Alavas/Modbus_Datalogger/Photos/DSC_0623.jpg

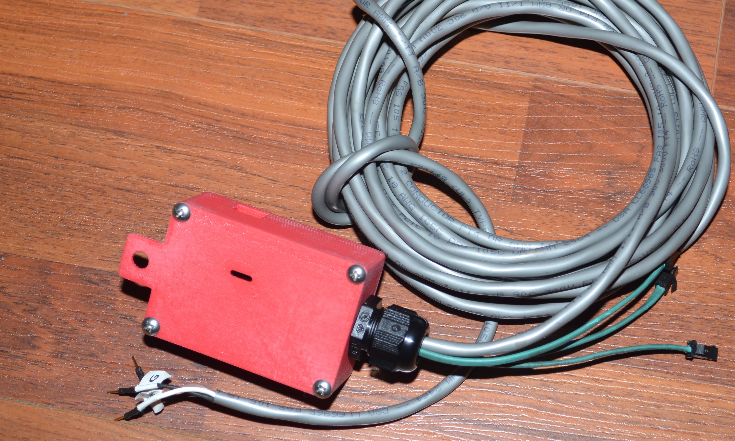
Photos/DSC_0623.jpg
