Alavas/Modbus_Datalogger/Photos/DSC_0625.jpg

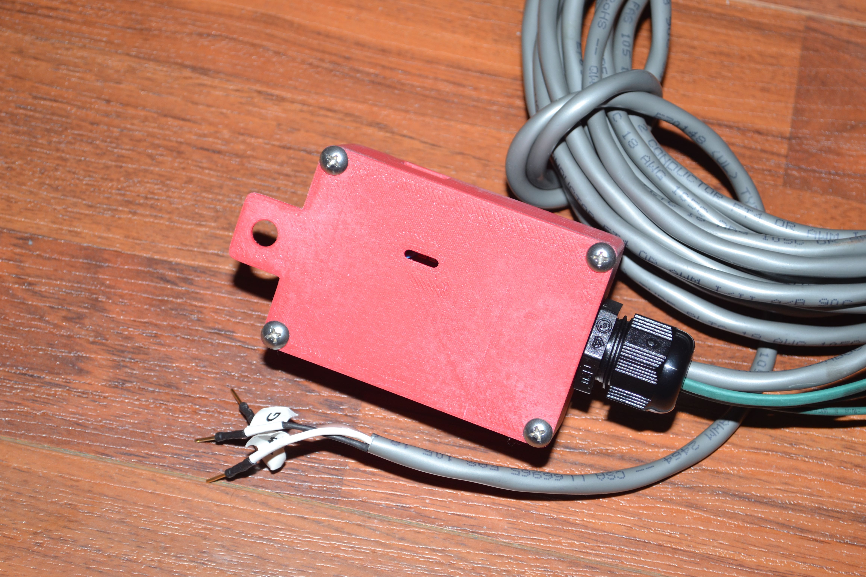
Photos/DSC_0625.jpg
