Alavas/Modbus_Datalogger/Photos/DSC_0633.jpg

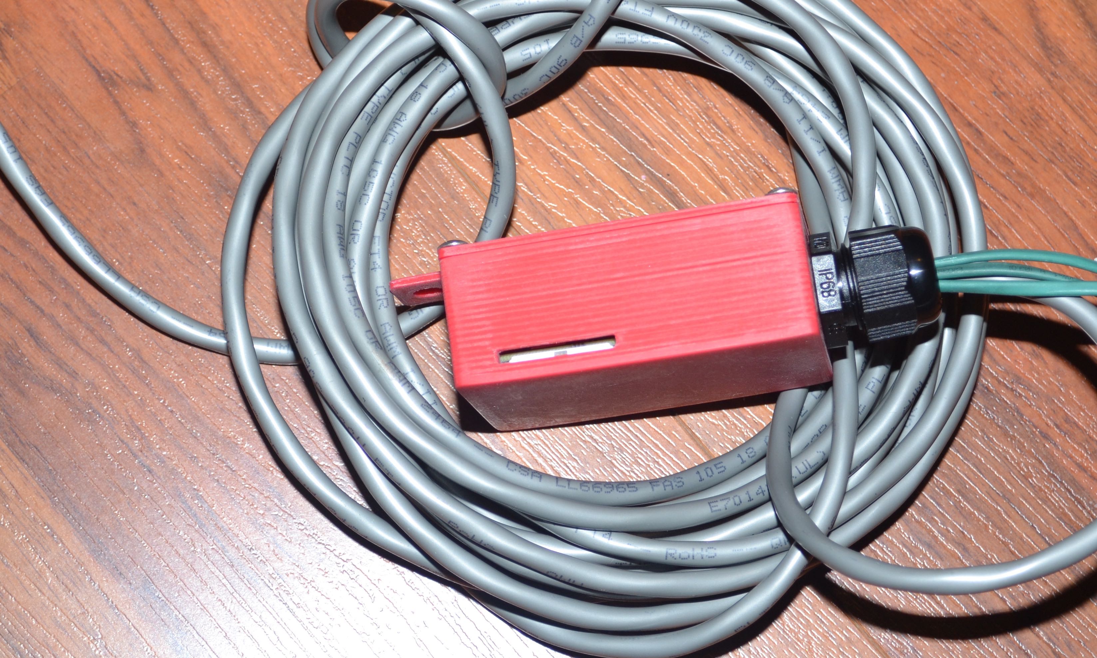
Photos/DSC_0633.jpg
