Alavas/Modbus_Datalogger/Photos/DSC_0634.jpg

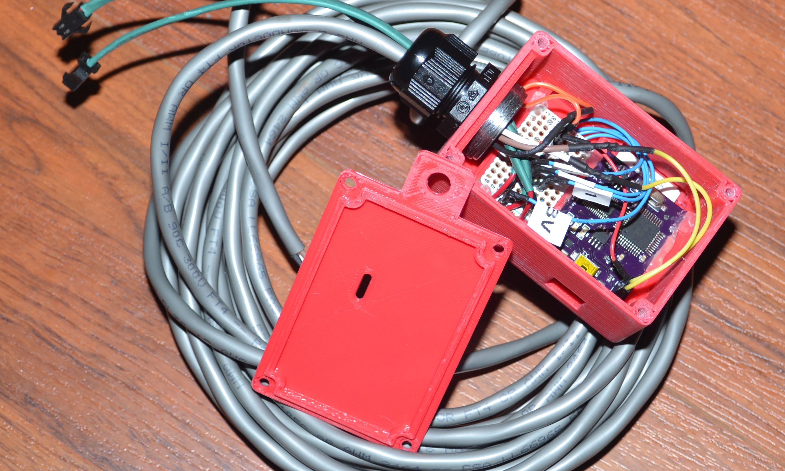
Photos/DSC_0634.jpg
