Alavas/Modbus_Datalogger/Photos/DSC_0635.jpg

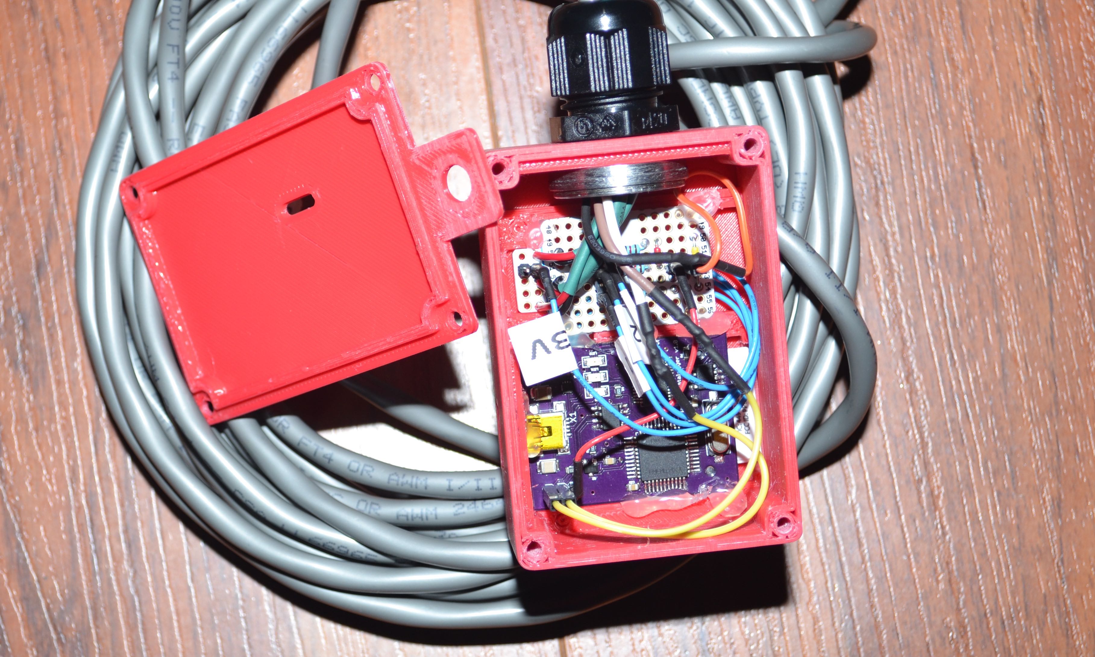
Photos/DSC_0635.jpg
